Ahmed-Mohiuddin-Shah/Arduino-Soldering-Station/src/pikachu.h

const unsigned char frame[][512] PROGMEM = {
{0x00, 0x00, 0x00, 0x00, 0x00, 0x00, 0x00, 0x00, 
0x00, 0x00, 0x00, 0x00, 0x00, 0x00, 0x00, 0x00, 
0x00, 0x00, 0x00, 0x00, 0x00, 0x00, 0x00, 0x00, 
0x00, 0x08, 0x00, 0x00, 0x02, 0x00, 0x00, 0x00, 
0x00, 0x00, 0x00, 0x00, 0x00, 0x00, 0x00, 0x00, 
0x00, 0x00, 0x00, 0x00, 0x00, 0x00, 0x00, 0x00, 
0x00, 0x42, 0x00, 0x00, 0x06, 0x10, 0x00, 0x00, 
0x00, 0x42, 0x00, 0x00, 0x43, 0x00, 0x00, 0x00, 
0x00, 0x1c, 0x00, 0x00, 0x07, 0x00, 0x00, 0x00, 
0x00, 0x1e, 0x80, 0x01, 0x0f, 0x00, 0x00, 0x00, 
0x00, 0x3f, 0x00, 0x00, 0x1f, 0x40, 0x00, 0x00, 
0x00, 0x5f, 0x80, 0x42, 0x3f, 0x40, 0x00, 0x00, 
0x00, 0x5f, 0xc0, 0x40, 0x7f, 0x40, 0x00, 0x00, 
0x00, 0x5c, 0x40, 0x40, 0xfc, 0x00, 0x00, 0x00, 
0x00, 0x38, 0x07, 0xcf, 0xfc, 0x00, 0x00, 0x00, 
0x00, 0x20, 0x07, 0xff, 0xfc, 0x00, 0x00, 0x00, 
0x00, 0x00, 0x3c, 0x3f, 0x9a, 0x00, 0x00, 0x00, 
0x00, 0x00, 0x78, 0x1f, 0xc0, 0x00, 0x30, 0x00, 
0x00, 0x23, 0xfa, 0x1f, 0xe0, 0x00, 0x40, 0x00, 
0x00, 0x1f, 0xf8, 0x1f, 0xe0, 0x00, 0x40, 0x00, 
0x00, 0x1f, 0xf8, 0x1f, 0xe0, 0x00, 0x00, 0x00, 
0x00, 0x5f, 0xfc, 0x3f, 0xfa, 0x00, 0x00, 0x00, 
0x00, 0x1b, 0xfe, 0x73, 0xfa, 0x00, 0x27, 0x00, 
0x00, 0x19, 0xff, 0xe3, 0xfa, 0x00, 0x24, 0x80, 
0x03, 0x3f, 0xff, 0xc0, 0xe2, 0x00, 0xdb, 0xe0, 
0x03, 0x78, 0x7b, 0xc0, 0xc3, 0x00, 0xdb, 0xe0, 
0x01, 0xf8, 0x39, 0xc0, 0x80, 0x00, 0xff, 0xe0, 
0x00, 0xe0, 0x07, 0xe1, 0x1f, 0x40, 0xff, 0xc0, 
0x00, 0xe0, 0x07, 0xe3, 0x5f, 0x40, 0xff, 0x80, 
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
0x00, 0x47, 0xff, 0xe0, 0x3f, 0x00, 0x3f, 0x80, 
0x00, 0x47, 0xff, 0xe0, 0x3f, 0x00, 0x3f, 0x80, 
0x00, 0x5f, 0xff, 0xc3, 0xff, 0xe0, 0x1f, 0x00, 
0x00, 0x1f, 0xff, 0xdf, 0xff, 0xe0, 0x7e, 0xe0, 
0x00, 0x3f, 0xff, 0x9f, 0xff, 0xe0, 0xfc, 0x00, 
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

};
